AaroSnid/Digital-Etch-A-Sketch/Media/Rev1/12068906A-Y3/1.jpg

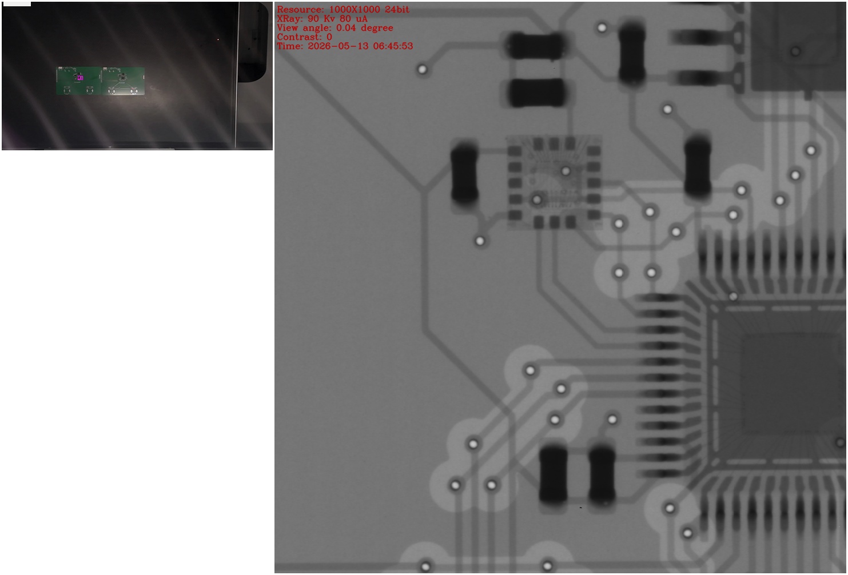
Media/Rev1/12068906A-Y3/1.jpg
